NeuronRobotics/ServoStock-hw/ServoStock/Axis/Rod.stl

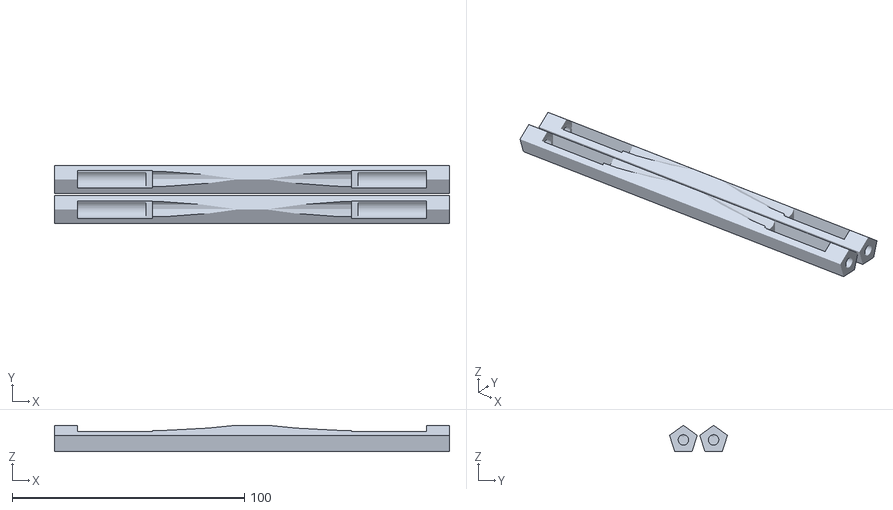
[picture p15: CAD file, 2014-07-28]
ServoStock/Axis/Rod.stl
170.0 x 25.0 x 11.4
