NeuronRobotics/ServoStock-hw/ServoStock/ContinuousBed/CanvasPulleyPrintBed.stl

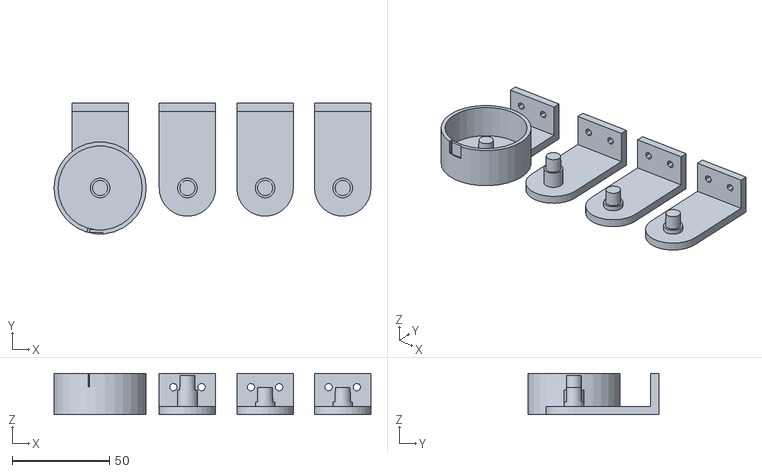
[picture p16: CAD file, 2014-09-04]
ServoStock/ContinuousBed/CanvasPulleyPrintBed.stl
163.3 x 67.3 x 21.4
