NeuronRobotics/ServoStock-hw/ServoStock/Extruder/Depricated/BusinessCardHolder2.stl

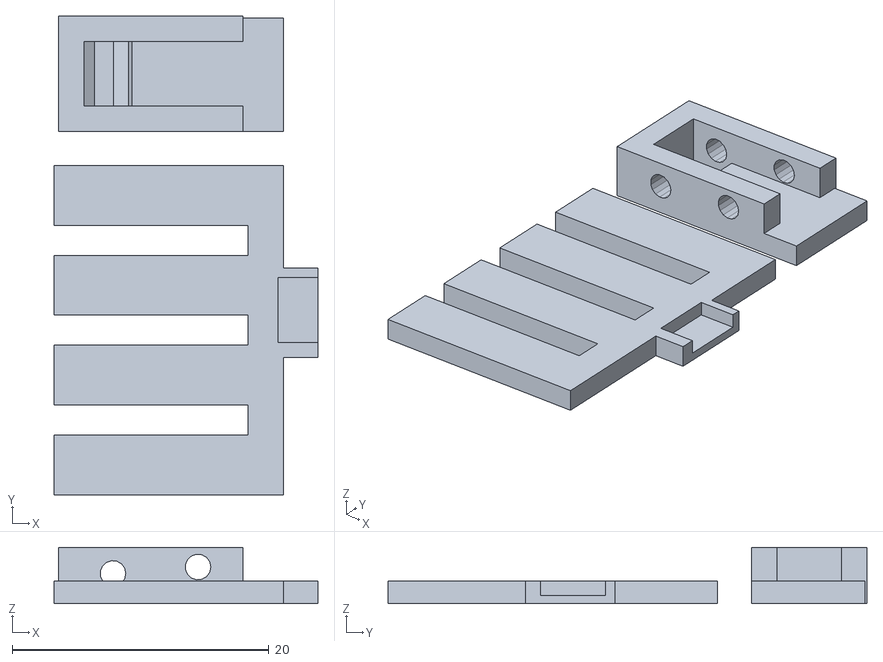
[picture p17: CAD file, 2014-07-28]
ServoStock/Extruder/Depricated/BusinessCardHolder2.stl
20.5 x 37.4 x 4.38
