NeuronRobotics/ServoStock-hw/ServoStock/Extruder/printBed/WormTopWPI.STL

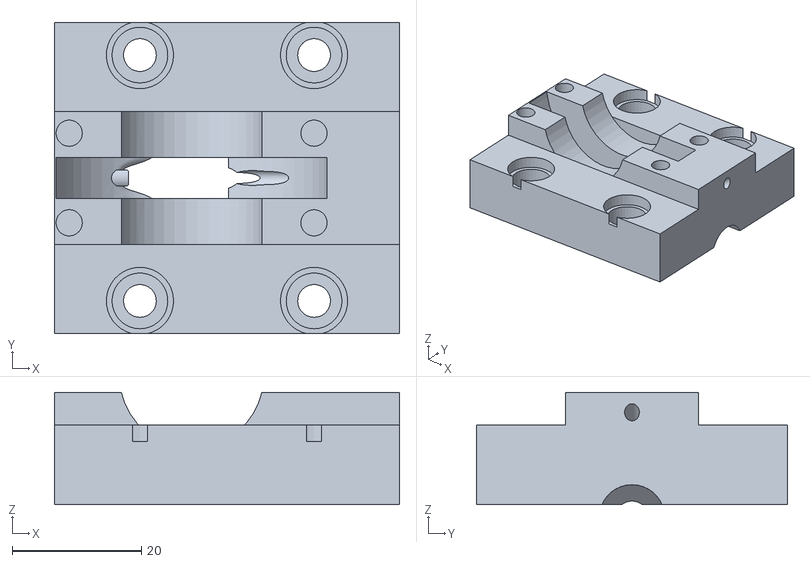
[picture p18: CAD file, 2014-09-12]
ServoStock/Extruder/printBed/WormTopWPI.STL
53.5 x 48.3 x 17.4
