NeuronRobotics/ServoStock-hw/ServoStock/Axis/Slider.stl

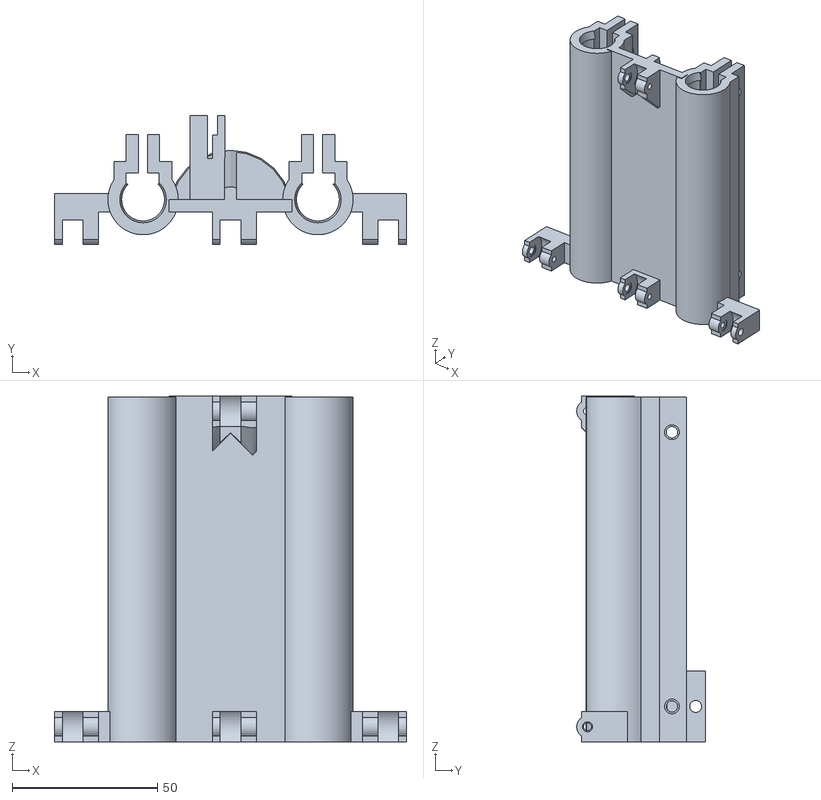
[picture p19: CAD file, 2014-06-01]
ServoStock/Axis/Slider.stl
121.0 x 44.3 x 118.9
