NeuronRobotics/ServoStock-hw/ServoStock/ContinuousBed/CanvasPulleyIdle.stl

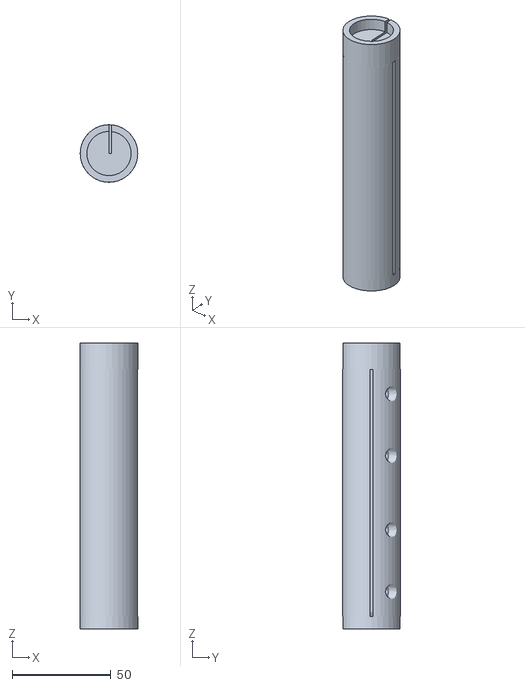
[picture p20: CAD file, 2014-09-04]
ServoStock/ContinuousBed/CanvasPulleyIdle.stl
29.1 x 29.1 x 144.5
