NeuronRobotics/ServoStock-hw/ServoStock/Extruder/Depricated/BusinessCardHolder.stl

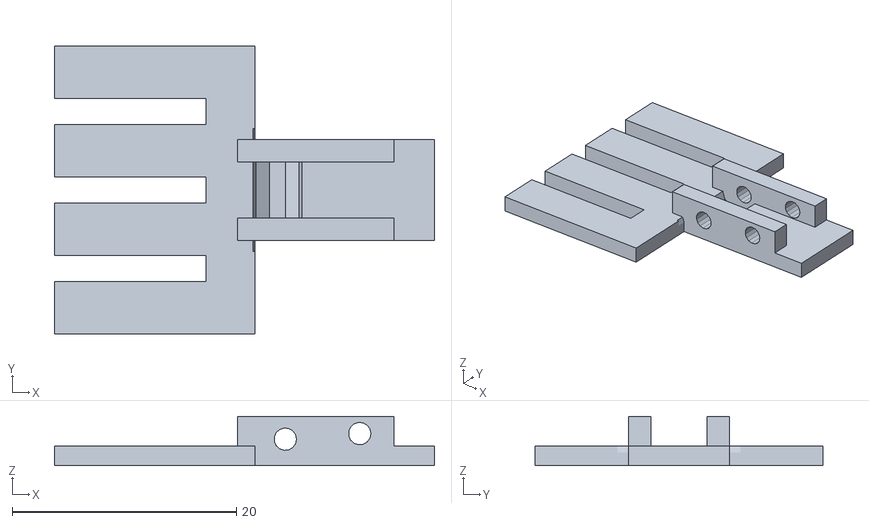
[picture p21: CAD file, 2014-07-28]
ServoStock/Extruder/Depricated/BusinessCardHolder.stl
33.9 x 25.7 x 4.38
