NeuronRobotics/ServoStock-hw/ServoStock/Extruder/printBed/Worm Bottom.STL

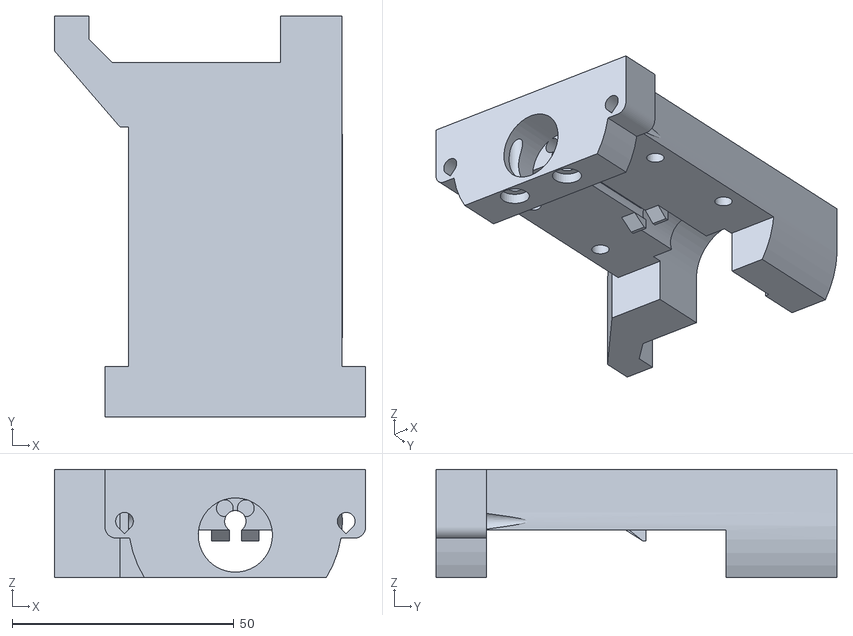
[picture p22: CAD file, 2014-09-12]
ServoStock/Extruder/printBed/Worm Bottom.STL
70.2 x 90.4 x 24.4
