NeuronRobotics/ServoStock-hw/ServoStock/ContinuousBed/CanvasPulley.stl

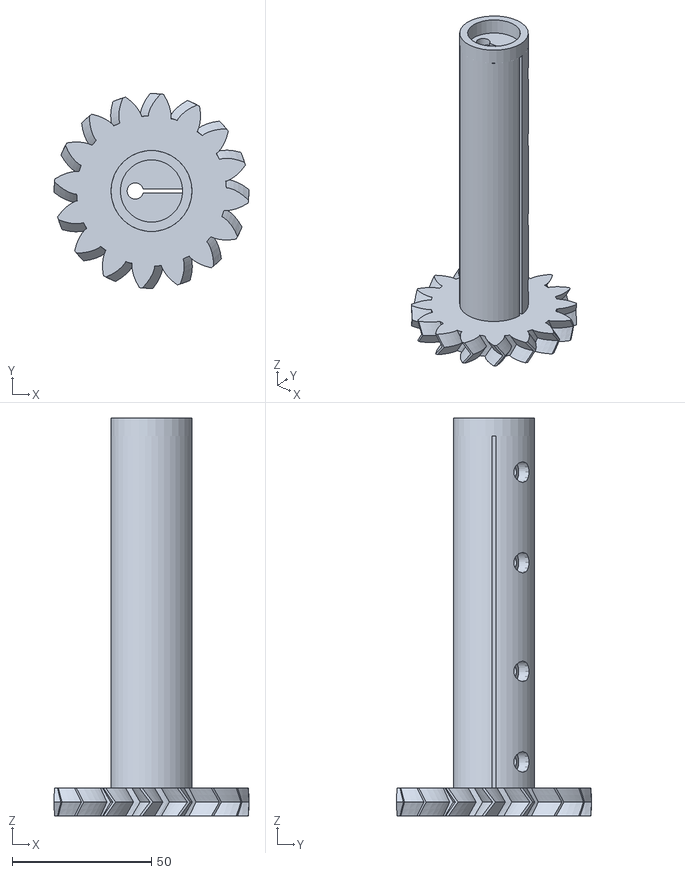
[picture p23: CAD file, 2014-08-25]
ServoStock/ContinuousBed/CanvasPulley.stl
70.0 x 70.0 x 143.0
