NeuronRobotics/ServoStock-hw/ServoStock/Axis/Clips.scad

use <Parameters.scad>
use <../../../Vitamins/Vitamins/Structural/SteelRod/8mm_Rod_Vitamin.scad>
use <../../../Vitamins/Vitamins/Actuators/StandardServo/StandardServo_Vitamin.scad>
use <../../../Vitamins/Vitamins/Fasteners/ScrewsAsBolts/High_Low_Screw_As_Bolt_Vitamin.scad>
use <../../../Vitamins/Vitamins/Fasteners/Screws/High_Low_Screw_Vitamin.scad>
use <../../../Vitamins/Vitamins/Structural/SealedBearings/SealedBearing608_Vitamin.scad>


function BearingBracketHeight()=608BallBearingDiam()*1.5;
function SlotWidth()= PlasticWidth()/2;
function ClipWidth()=StandardServoHeightAbvWings()-1.5;

function getClipHolePlacement()=PlasticWidth()+8mmRodDiameter(.8)/4-ClipWidth();

module placeClipMountHoleCenter(){
	translate(	[-12,0,0]){
			for (i = [0 : $children-1]){
				translate([	getClipHolePlacement(),
							0,
							0]){
					child(i);
				}
			 }	
		}
}

module placeRodHoleCenter(){
	translate([	getClipHolePlacement(),
				0,
				0]
	){
		for (i = [0 : $children-1]){
			 child(i);
		 }
			
	}
}


//This makes a single clip
module clip(Height = MotorBracketHeight())
{
	difference()
	{
		translate([0,-SideWidth()/2,0])
		{	
			difference()
			{
				//this makes the basic curved rectangle shape of the clip
				union()
				{
					translate([-5.5-ClipWidth(),0,0])
							cube([(SideWidth()*2+5.5),SideWidth(),Height]);
					translate([-5.5-ClipWidth(),SideWidth()/2,0])
					{
						cylinder(h=Height,r=SideWidth()/2);
					}
				}

				//This makes the holes for the structural rod
				translate([	0,SideWidth()/2,-1]){
					placeRodHoleCenter(){
						cylinder(h=Height+2, r=8mmRodDiameter(.8)/2, $fn=50);
					}
					//This makes the screwholes for the bed mount
					placeClipMountHoleCenter(){
						cylinder(h=Height+3, r=HiLoScrewDiameter(.6)/2, $fn=50);
					}
				}
				//This makes the slot for the clip
				translate([	8mmRodDiameter(.8)/2+8mmRodDiameter(.8)/4+1-ClipWidth(),
				           	SideWidth()/2-PlasticWidth()/4,
				           	-1])
				{
					cube([SideWidth()*2-SideWidth()/2+PlasticWidth(),SlotWidth(),Height+2]);
				}


			} 	
		}	
	}	
}


module sidebolts(Height = MotorBracketHeight())
{
	union()
	{

		//These make the boltholes for the clip
		//uncomment these translates and rotates when you're ready to 
		//translate([SideWidth()*2-PlasticWidth()*1.5,-PlasticWidth()-HiLoBoltHeadHeight()/2-1,Height/3])
		//{
		//	rotate([90,0,0])
		//	{
		translate([	SideWidth()*2-PlasticWidth()*1.5,
		           	PlasticWidth()+HiLoBoltHeadHeight()/2+1-13,
		           	Height/3])
		{
			rotate([-90,0,180])
			{
				HiLoBolt(.4, PlasticWidth());
			}
		}
		//translate([SideWidth()*2-PlasticWidth()*1.5,-PlasticWidth()-HiLoBoltHeadHeight()/2-1,2*Height/3])
		//{
		//	rotate([90,0,0])
		//	{
		translate([	SideWidth()*2-PlasticWidth()*1.5,
		           	PlasticWidth()+HiLoBoltHeadHeight()/2+1-13,
		           	2*Height/3])
		{
			rotate([-90,0,180])
			{
				HiLoBolt(.4, PlasticWidth());
			}
		}		
	}
}

module bolts(Height = MotorBracketHeight())
{
	
	union()
	{
		sidebolts(Height);
		translate([0, ZrodSpacing(),0])
		{
			mirror([0,1,0])
			{
				sidebolts(Height);
			}
		}
	}
}
		
module localClips(height=10){
	translate([0,-ZrodSpacing()/2, 0])
	{
		difference()
		{
			union()
			{
	//this draws the clips themselves
				clip(height);
				translate([0,ZrodSpacing(),0])
				{
					clip(height);
				}
				translate([-ClipWidth(),8mmRodDiameter(.8)/2, 0])
//this draws the box between the clips
				{
					cube([ClipWidth(), ZrodSpacing()-8mmRodDiameter(.8),height]);
				}
			}
			translate([-ClipWidth(),0, 0])
				bolts(height);
		}
	}

}

//This module calls the clips and makes the box between them. If true, it makes the bottom set, and if false it makes the top set (which is shorter)
module Clips(MotorHeight=true)
{
	//This part of the if statement makes the bottom clips
	if(MotorHeight==true){
		localClips(MotorBracketHeight());
	//this is same as above, except it makes the top clips	
	}else{
		localClips(BearingBracketHeight());		
	}
}



Clips(false);
