NeuronRobotics/ServoStock-hw/ServoStock/Extruder/wormtownbottom.scad

//this is the bottom piece of the wormtown extruder

$fn=100;

use <../../../Vitamins/Vitamins/Actuators/StandardServo/StandardServo_Vitamin.scad>
use <../../../Vitamins/Vitamins/Electronics/Hot_Ends/PrintrBotJHeadHotEnd_Vitamin.scad>
use <../../../Vitamins/Vitamins/Fasteners/Screws/High_Low_Screw_Vitamin.scad>
use <../../../Vitamins/Vitamins/Fasteners/Screws/ExtruderWoodScrew_Vitamin.scad>
use <../../../Vitamins/Vitamins/Fasteners/ScrewsAsBolts/High_Low_Screw_As_Bolt_Vitamin.scad>
