NeuronRobotics/ServoStock-hw/ServoStock/Extruder/Depricated/ExtruderPrintBed.scad

use <ExtruderMKII.scad>;
use <ExtruderIdlerWheel.scad>;
use <Extruder_Encoder_Keepaway.scad>;

ExtruderPrint();
